akkako/akaLinkPro/firmware/application_5301/boards/akaLinkPro/pinmux.c

/*
 * Copyright (c) 2026 HPMicro
 *
 * SPDX-License-Identifier: BSD-3-Clause
 *
 */

/*
 * Note:
 * PY and PZ IOs: if any SOC pin function needs to be routed to these IOs,
 * besides of IOC, PIOC/BIOC needs to be configured SOC_GPIO_X_xx, so that
 * expected SoC function can be enabled on these IOs.
 */

#include "pinmux.h"
#include "board.h"
#include "hpm_trgm_drv.h"
#include "hpm_gpio_drv.h"
#include "hpm_gpiom_drv.h"

/* 5V output enable for the level shifter supply (active high). */
#define POWER_5V_EN_PIN IOC_PAD_PB13

/* Status LEDs (active high). */
#define LED1_PIN IOC_PAD_PB11
#define LED2_PIN IOC_PAD_PB12

/* External reference voltage sense (10k/10k divider), ADC0.2. */
#define ADC_VREF_PIN IOC_PAD_PB10


static void gpiom_config_pin_to_gpio0(uint16_t gpio_index)
{
    gpiom_set_pin_controller(HPM_GPIOM,
                             GPIO_GET_PORT_INDEX(gpio_index),
                             GPIO_GET_PIN_INDEX(gpio_index),
                             gpiom_soc_gpio0);
    gpiom_enable_pin_visibility(HPM_GPIOM,
                                GPIO_GET_PORT_INDEX(gpio_index),
                                GPIO_GET_PIN_INDEX(gpio_index),
                                gpiom_soc_gpio0);
}

static void init_unused_pin_as_input_pull_down(uint16_t gpio_index)
{
    HPM_IOC->PAD[gpio_index].FUNC_CTL = IOC_PAD_FUNC_CTL_ALT_SELECT_SET(0);
    HPM_IOC->PAD[gpio_index].PAD_CTL = IOC_PAD_PAD_CTL_PE_SET(1) | IOC_PAD_PAD_CTL_PS_SET(0);

    gpiom_config_pin_to_gpio0(gpio_index);
    gpio_set_pin_input(HPM_GPIO0, GPIO_GET_PORT_INDEX(gpio_index), GPIO_GET_PIN_INDEX(gpio_index));
    
}

static void init_unused_pin_as_input_no_pull(uint16_t gpio_index)
{
    HPM_IOC->PAD[gpio_index].FUNC_CTL = IOC_PAD_FUNC_CTL_ALT_SELECT_SET(0);
    HPM_IOC->PAD[gpio_index].PAD_CTL = 0;

    gpiom_config_pin_to_gpio0(gpio_index);
    gpio_set_pin_input(HPM_GPIO0, GPIO_GET_PORT_INDEX(gpio_index), GPIO_GET_PIN_INDEX(gpio_index));
    
}

/**
 * @brief Set PY00-PY05 default function to PGPIO
 * @param None
 */
void init_py_pins_as_pgpio(void)
{
    HPM_PIOC->PAD[IOC_PAD_PY00].FUNC_CTL = PIOC_PY00_FUNC_CTL_PGPIO_Y_00;
    HPM_PIOC->PAD[IOC_PAD_PY01].FUNC_CTL = PIOC_PY01_FUNC_CTL_PGPIO_Y_01;
}

/**
 * @brief Init UART0 Console print pin
 * @param None
 */
void init_uart0_pins(void)
{
    HPM_IOC->PAD[IOC_PAD_PA00].FUNC_CTL = IOC_PA00_FUNC_CTL_UART0_TXD;
    HPM_IOC->PAD[IOC_PAD_PA01].FUNC_CTL = IOC_PA01_FUNC_CTL_UART0_RXD;
}

/*
 * configure pad setting: pull enable and pull down, schmitt trigger enable
 * enable schmitt trigger to eliminate jitter of pin used as button
 */
void init_button_pins(void)
{
    /* Button */
    HPM_IOC->PAD[IOC_PAD_PA10].FUNC_CTL = IOC_PAD_FUNC_CTL_ALT_SELECT_SET(0);
    HPM_IOC->PAD[IOC_PAD_PA10].PAD_CTL = IOC_PAD_PAD_CTL_HYS_SET(1) | IOC_PAD_PAD_CTL_PE_SET(1) | IOC_PAD_PAD_CTL_PS_SET(0);
}

/**
 * @brief Set the 5V output enable pin (PB13, active high).
 * @param on 1 = enable 5V output, 0 = disable
 */
void board_set_5v_output(uint8_t on)
{
    gpio_write_pin(HPM_GPIO0, GPIO_GET_PORT_INDEX(POWER_5V_EN_PIN), GPIO_GET_PIN_INDEX(POWER_5V_EN_PIN), on ? 1 : 0);
}

/**
 * @brief Init power control pin and enable the 5V output by default.
 * @param None
 */
void init_power_pins(void)
{
    HPM_IOC->PAD[POWER_5V_EN_PIN].FUNC_CTL = IOC_PAD_FUNC_CTL_ALT_SELECT_SET(0);
    HPM_IOC->PAD[POWER_5V_EN_PIN].PAD_CTL =
        IOC_PAD_PAD_CTL_HYS_SET(0) | // schmitt trigger disable
        IOC_PAD_PAD_CTL_PRS_SET(0) | // pull resistor 100k
        IOC_PAD_PAD_CTL_PS_SET(0) |  // pull down
        IOC_PAD_PAD_CTL_PE_SET(0) |  // pull disable
        IOC_PAD_PAD_CTL_KE_SET(0) |  // keeper disable
        IOC_PAD_PAD_CTL_OD_SET(0) |  // open drain disable
        IOC_PAD_PAD_CTL_SR_SET(1) |  // fast slew rate
        IOC_PAD_PAD_CTL_SPD_SET(3) | // fastest slew rate
        IOC_PAD_PAD_CTL_DS_SET(4);   // drive strength 39 ohm(3.3V)

    gpiom_config_pin_to_gpio0(POWER_5V_EN_PIN);
    gpio_set_pin_output(HPM_GPIO0, GPIO_GET_PORT_INDEX(POWER_5V_EN_PIN), GPIO_GET_PIN_INDEX(POWER_5V_EN_PIN));
    board_set_5v_output(1);
}

/**
 * @brief Init the status LED pins as push-pull GPIO outputs, both off.
 * @param None
 */
void init_led_pins(void)
{
    const uint16_t leds[2] = {LED1_PIN, LED2_PIN};

    for (uint32_t i = 0; i < 2; i++)
    {
        HPM_IOC->PAD[leds[i]].FUNC_CTL = IOC_PAD_FUNC_CTL_ALT_SELECT_SET(0);
        HPM_IOC->PAD[leds[i]].PAD_CTL =
            IOC_PAD_PAD_CTL_HYS_SET(0) | // schmitt trigger disable
            IOC_PAD_PAD_CTL_PRS_SET(0) | // pull resistor 100k
            IOC_PAD_PAD_CTL_PS_SET(0) |  // pull down
            IOC_PAD_PAD_CTL_PE_SET(0) |  // pull disable
            IOC_PAD_PAD_CTL_KE_SET(0) |  // keeper disable
            IOC_PAD_PAD_CTL_OD_SET(0) |  // open drain disable
            IOC_PAD_PAD_CTL_SR_SET(1) |  // fast slew rate
            IOC_PAD_PAD_CTL_SPD_SET(3) | // fastest slew rate
            IOC_PAD_PAD_CTL_DS_SET(4);   // drive strength 39 ohm(3.3V)

        gpiom_config_pin_to_gpio0(leds[i]);
        gpio_set_pin_output(HPM_GPIO0, GPIO_GET_PORT_INDEX(leds[i]), GPIO_GET_PIN_INDEX(leds[i]));
        gpio_write_pin(HPM_GPIO0, GPIO_GET_PORT_INDEX(leds[i]), GPIO_GET_PIN_INDEX(leds[i]), 0);
    }
}

/**
 * @brief Init the external reference sense pin as ADC analog input.
 * @param None
 */
void init_adc_vref_pin(void)
{
    HPM_IOC->PAD[ADC_VREF_PIN].FUNC_CTL = IOC_PAD_FUNC_CTL_ANALOG_MASK;
}

/**
 * @brief Init USB0 pins
 * @param None
 */
void init_usb0_pins(void)
{
    HPM_IOC->PAD[IOC_PAD_PA24].FUNC_CTL = IOC_PAD_FUNC_CTL_ANALOG_MASK;

    HPM_IOC->PAD[IOC_PAD_PA25].FUNC_CTL = IOC_PAD_FUNC_CTL_ANALOG_MASK;

    /* USB0_ID */
    HPM_IOC->PAD[IOC_PAD_PY00].FUNC_CTL = IOC_PY00_FUNC_CTL_USB0_ID;
    HPM_PIOC->PAD[IOC_PAD_PY00].FUNC_CTL = PIOC_PY00_FUNC_CTL_SOC_GPIO_Y_00;

    /* USB0_OC */
    HPM_IOC->PAD[IOC_PAD_PY01].FUNC_CTL = IOC_PY01_FUNC_CTL_USB0_OC;
    HPM_PIOC->PAD[IOC_PAD_PY01].FUNC_CTL = PIOC_PY01_FUNC_CTL_SOC_GPIO_Y_01;
}

/**
 * @brief Init UART3 as VCOM port
 * @param None
 */
void init_uart3_pins_as_uart(void)
{
    // HPM_IOC->PAD[IOC_PAD_PB15].FUNC_CTL = IOC_PB15_FUNC_CTL_UART3_TXD;
    // HPM_IOC->PAD[IOC_PAD_PB14].FUNC_CTL = IOC_PB14_FUNC_CTL_UART3_RXD;
}

/*
 * for uart_lin case, need to configure pin as gpio to sent break signal
 * pull-up
 */
void init_uart3_pin_as_gpio_low(void)
{
    // HPM_IOC->PAD[BOARD_PIN_UART_TXD].FUNC_CTL = IOC_PAD_FUNC_CTL_ALT_SELECT_SET(0);
    // HPM_IOC->PAD[BOARD_PIN_UART_TXD].PAD_CTL = IOC_PAD_PAD_CTL_PE_SET(1) | IOC_PAD_PAD_CTL_PS_SET(0);

    // HPM_IOC->PAD[BOARD_PIN_UART_RXD].FUNC_CTL = IOC_PAD_FUNC_CTL_ALT_SELECT_SET(0);
    // HPM_IOC->PAD[BOARD_PIN_UART_RXD].PAD_CTL = IOC_PAD_PAD_CTL_PE_SET(1) | IOC_PAD_PAD_CTL_PS_SET(0);

    // HPM_IOC->PAD[BOARD_PIN_UART_RTS].FUNC_CTL = IOC_PAD_FUNC_CTL_ALT_SELECT_SET(0);
    // HPM_IOC->PAD[BOARD_PIN_UART_RTS].PAD_CTL = IOC_PAD_PAD_CTL_PE_SET(1) | IOC_PAD_PAD_CTL_PS_SET(0);

    // HPM_IOC->PAD[BOARD_PIN_UART_DTR].FUNC_CTL = IOC_PAD_FUNC_CTL_ALT_SELECT_SET(0);
    // HPM_IOC->PAD[BOARD_PIN_UART_DTR].PAD_CTL = IOC_PAD_PAD_CTL_PE_SET(1) | IOC_PAD_PAD_CTL_PS_SET(0);

    // gpiom_config_pin_to_gpio0(BOARD_PIN_UART_TXD);
    // gpiom_config_pin_to_gpio0(BOARD_PIN_UART_RXD);
    // gpiom_config_pin_to_gpio0(BOARD_PIN_UART_RTS);
    // gpiom_config_pin_to_gpio0(BOARD_PIN_UART_DTR);

    // gpio_set_pin_output(HPM_GPIO0, GPIO_GET_PORT_INDEX(BOARD_PIN_UART_TXD), GPIO_GET_PIN_INDEX(BOARD_PIN_UART_TXD));
    // gpio_set_pin_output(HPM_GPIO0, GPIO_GET_PORT_INDEX(BOARD_PIN_UART_RTS), GPIO_GET_PIN_INDEX(BOARD_PIN_UART_RTS));
    // gpio_set_pin_output(HPM_GPIO0, GPIO_GET_PORT_INDEX(BOARD_PIN_UART_DTR), GPIO_GET_PIN_INDEX(BOARD_PIN_UART_DTR));
    // gpio_set_pin_input(HPM_GPIO0, GPIO_GET_PORT_INDEX(BOARD_PIN_UART_RXD), GPIO_GET_PIN_INDEX(BOARD_PIN_UART_RXD));

    // gpio_write_pin(HPM_GPIO0, GPIO_GET_PORT_INDEX(BOARD_PIN_UART_TXD), GPIO_GET_PIN_INDEX(BOARD_PIN_UART_TXD), 0);
    // gpio_write_pin(HPM_GPIO0, GPIO_GET_PORT_INDEX(BOARD_PIN_UART_RTS), GPIO_GET_PIN_INDEX(BOARD_PIN_UART_RTS), 0);
    // gpio_write_pin(HPM_GPIO0, GPIO_GET_PORT_INDEX(BOARD_PIN_UART_DTR), GPIO_GET_PIN_INDEX(BOARD_PIN_UART_DTR), 0);
}

/*
 * @brief Init unused pins as input
 * @param None
 */
void init_unused_pin_as_input(void)
{
    // init_unused_pin_as_input_pull_down(BOARD_PIN_UNUSED_PORTEN);
    // init_unused_pin_as_input_pull_down(BOARD_PIN_UNUSED_PWM);
    // init_unused_pin_as_input_pull_down(BOARD_PIN_UNUSED_CS1);
    // init_unused_pin_as_input_pull_down(BOARD_PIN_UNUSED_CS2);
    // init_unused_pin_as_input_pull_down(BOARD_PIN_UNUSED_PEN);
    // init_unused_pin_as_input_pull_down(BOARD_PIN_UNUSED_VREF);
    // init_unused_pin_as_input_pull_down(BOARD_PIN_UNUSED_TVCC);
    // init_unused_pin_as_input_no_pull(BOARD_PIN_UNUSED_JTCK);
}

/**
 * @brief Init JTAG SWD pins as default state
 * @param None
 */
void init_jtag_swd_pin(void)
{
}
