akkako/akaLinkPro/firmware/application_5301/src/dap/SW_DP/SW_DP.c

/*
 * Copyright (c) 2013-2017 ARM Limited. All rights reserved.
 *
 * SPDX-License-Identifier: Apache-2.0
 *
 * Licensed under the Apache License, Version 2.0 (the License); you may
 * not use this file except in compliance with the License.
 * You may obtain a copy of the License at
 *
 * www.apache.org/licenses/LICENSE-2.0
 *
 * Unless required by applicable law or agreed to in writing, software
 * distributed under the License is distributed on an AS IS BASIS, WITHOUT
 * WARRANTIES OR CONDITIONS OF ANY KIND, either express or implied.
 * See the License for the specific language governing permissions and
 * limitations under the License.
 *
 * ----------------------------------------------------------------------
 *
 * $Date:        1. December 2017
 * $Revision:    V2.0.0
 *
 * Project:      CMSIS-DAP Source
 * Title:        SW_DP.c CMSIS-DAP SW DP I/O
 *
 *---------------------------------------------------------------------------*/

#include "DAP_config.h"
#include "DAP.h"
#include "SW_DP.h"
#include "hpm_common.h"

#define SWJ_SEQUENCE_OFFSET_60M 0x00000000
#define SWD_WRITE_OFFSET_60M 0x000000fc
#define SWD_READ_OFFSET_60M 0x0000053c

#define SWJ_SEQUENCE_OFFSET_45M 0x00000000
#define SWD_WRITE_OFFSET_45M 0x00000120
#define SWD_READ_OFFSET_45M 0x0000060c

#define SWJ_SEQUENCE_OFFSET_36M 0x00000000
#define SWD_WRITE_OFFSET_36M 0x00000144
#define SWD_READ_OFFSET_36M 0x000006e0

#define SWJ_SEQUENCE_OFFSET_30M 0x00000000
#define SWD_WRITE_OFFSET_30M 0x0000016c
#define SWD_READ_OFFSET_30M 0x000007c4

#define SWJ_SEQUENCE_OFFSET_20M 0x00000000
#define SWD_WRITE_OFFSET_20M 0x000001d8
#define SWD_READ_OFFSET_20M 0x00000a54

#define SWJ_SEQUENCE_OFFSET_SLOW 0x00000010
#define SWD_WRITE_OFFSET_SLOW 0x00000138
#define SWD_READ_OFFSET_SLOW 0x00000620

// clang-format off
const uint8_t swd_func_60m[2584] =
{
	0xB7, 0x02, 0x0C, 0x00, 0x37, 0x03, 0x00, 0x40, 0xB7, 0x03, 0x00, 0x08, 0x93, 0x56, 0x35, 0x00,
    0x13, 0x77, 0x75, 0x00, 0xE1, 0xC2, 0x03, 0xC8, 0x05, 0x00, 0x85, 0x05, 0x13, 0x7E, 0x18, 0x00,
    0x72, 0x0E, 0x33, 0x6E, 0x6E, 0x00, 0x23, 0xA0, 0xC2, 0x11, 0x13, 0x58, 0x18, 0x00, 0x13, 0x7E,
    0x18, 0x00, 0x23, 0xA2, 0x72, 0x10, 0x72, 0x0E, 0x33, 0x6E, 0x6E, 0x00, 0x23, 0xA0, 0xC2, 0x11,
    0x13, 0x58, 0x18, 0x00, 0x13, 0x7E, 0x18, 0x00, 0x23, 0xA2, 0x72, 0x10, 0x72, 0x0E, 0x33, 0x6E,
    0x6E, 0x00, 0x23, 0xA0, 0xC2, 0x11, 0x13, 0x58, 0x18, 0x00, 0x13, 0x7E, 0x18, 0x00, 0x23, 0xA2,
    0x72, 0x10, 0x72, 0x0E, 0x33, 0x6E, 0x6E, 0x00, 0x23, 0xA0, 0xC2, 0x11, 0x13, 0x58, 0x18, 0x00,
    0x13, 0x7E, 0x18, 0x00, 0x23, 0xA2, 0x72, 0x10, 0x72, 0x0E, 0x33, 0x6E, 0x6E, 0x00, 0x23, 0xA0,
    0xC2, 0x11, 0x13, 0x58, 0x18, 0x00, 0x13, 0x7E, 0x18, 0x00, 0x23, 0xA2, 0x72, 0x10, 0x72, 0x0E,
    0x33, 0x6E, 0x6E, 0x00, 0x23, 0xA0, 0xC2, 0x11, 0x13, 0x58, 0x18, 0x00, 0x13, 0x7E, 0x18, 0x00,
    0x23, 0xA2, 0x72, 0x10, 0x72, 0x0E, 0x33, 0x6E, 0x6E, 0x00, 0x23, 0xA0, 0xC2, 0x11, 0x13, 0x58,
    0x18, 0x00, 0x13, 0x7E, 0x18, 0x00, 0x23, 0xA2, 0x72, 0x10, 0x72, 0x0E, 0x33, 0x6E, 0x6E, 0x00,
    0x23, 0xA0, 0xC2, 0x11, 0x13, 0x58, 0x18, 0x00, 0x13, 0x7E, 0x18, 0x00, 0x23, 0xA2, 0x72, 0x10,
    0xFD, 0x16, 0xB1, 0xF2, 0x15, 0xC3, 0x03, 0xC8, 0x05, 0x00, 0x13, 0x7E, 0x18, 0x00, 0x72, 0x0E,
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

swd_sequence_ptr seq_func = NULL;
swd_write_ptr write_func = NULL;
swd_read_ptr read_func = NULL;

void SWD_DynamicLoad_Slow(void)
{
    memcpy(swd_ops, swd_func_slow, sizeof(swd_func_slow));
    __asm volatile("fence.i");

    seq_func = (swd_sequence_ptr)((uint32_t)swd_ops + SWJ_SEQUENCE_OFFSET_SLOW);
    write_func = (swd_write_ptr)((uint32_t)swd_ops + SWD_WRITE_OFFSET_SLOW);
    read_func = (swd_read_ptr)((uint32_t)swd_ops + SWD_READ_OFFSET_SLOW);
}

void SWD_DynamicLoad_60M(void)
{
    memcpy(swd_ops, swd_func_60m, sizeof(swd_func_60m));
    __asm volatile("fence.i");

    seq_func = (swd_sequence_ptr)((uint32_t)swd_ops + SWJ_SEQUENCE_OFFSET_60M);
    write_func = (swd_write_ptr)((uint32_t)swd_ops + SWD_WRITE_OFFSET_60M);
    read_func = (swd_read_ptr)((uint32_t)swd_ops + SWD_READ_OFFSET_60M);
}

void SWD_DynamicLoad_45M(void)
{
    memcpy(swd_ops, swd_func_45m, sizeof(swd_func_45m));
    __asm volatile("fence.i");

    seq_func = (swd_sequence_ptr)((uint32_t)swd_ops + SWJ_SEQUENCE_OFFSET_45M);
    write_func = (swd_write_ptr)((uint32_t)swd_ops + SWD_WRITE_OFFSET_45M);
    read_func = (swd_read_ptr)((uint32_t)swd_ops + SWD_READ_OFFSET_45M);
}

void SWD_DynamicLoad_36M(void)
{
    memcpy(swd_ops, swd_func_36m, sizeof(swd_func_36m));
    __asm volatile("fence.i");

    seq_func = (swd_sequence_ptr)((uint32_t)swd_ops + SWJ_SEQUENCE_OFFSET_36M);
    write_func = (swd_write_ptr)((uint32_t)swd_ops + SWD_WRITE_OFFSET_36M);
    read_func = (swd_read_ptr)((uint32_t)swd_ops + SWD_READ_OFFSET_36M);
}

void SWD_DynamicLoad_30M(void)
{
    memcpy(swd_ops, swd_func_30m, sizeof(swd_func_30m));
    __asm volatile("fence.i");

    seq_func = (swd_sequence_ptr)((uint32_t)swd_ops + SWJ_SEQUENCE_OFFSET_30M);
    write_func = (swd_write_ptr)((uint32_t)swd_ops + SWD_WRITE_OFFSET_30M);
    read_func = (swd_read_ptr)((uint32_t)swd_ops + SWD_READ_OFFSET_30M);
}

void SWD_DynamicLoad_20M(void)
{
    memcpy(swd_ops, swd_func_20m, sizeof(swd_func_20m));
    __asm volatile("fence.i");

    seq_func = (swd_sequence_ptr)((uint32_t)swd_ops + SWJ_SEQUENCE_OFFSET_20M);
    write_func = (swd_write_ptr)((uint32_t)swd_ops + SWD_WRITE_OFFSET_20M);
    read_func = (swd_read_ptr)((uint32_t)swd_ops + SWD_READ_OFFSET_20M);
}

#if ((DAP_SWD != 0) || (DAP_JTAG != 0))
/**
 * @brief Generate SWJ Sequence
 * @param count sequence bit count
 * @param data pointer to sequence bit data
 * @return none
 */
ATTR_RAMFUNC void SWJ_Sequence(uint32_t count, const uint8_t *data)
{
    seq_func(count, data, DAP_Data.clock_delay);
}
#endif

#if (DAP_SWD != 0)
/**
 * @brief Generate SWD Sequence
 * @param info sequence information
 * @param swdo pointer to SWDIO generated data
 * @param swdi pointer to SWDIO captured data
 * @return none
 */
ATTR_RAMFUNC void SWD_Sequence(uint32_t info, const uint8_t *swdo, uint8_t *swdi)
{
    // SWD_Sequence_GPIO_Fast(info, swdo, swdi);
    SWD_Sequence_GPIO_Slow(info, swdo, swdi);
}
#endif

/**
 * @brief SWD Write
 * @param request A[3:2] RnW APnDP
 * @param data DATA[31:0]
 * @return ACK[2:0]
 */
ATTR_RAMFUNC uint8_t SWD_Write(uint32_t request, uint32_t *data)
{
    uint8_t header = 0x81 | ((request & 0x0F) << 1) | (((request ^ (request >> 1) ^ (request >> 2) ^ (request >> 3)) & 1) << 5);

    uint8_t ack = write_func(header, data, DAP_Data.clock_delay);
    if (request & DAP_TRANSFER_TIMESTAMP)
    {
        DAP_Data.timestamp = TIMESTAMP_GET();
    }
    return ack;
}

/**
 * @brief SWD Read
 * @param request A[3:2] RnW APnDP
 * @param data DATA[31:0]
 * @return ACK[2:0]
 */
ATTR_RAMFUNC uint8_t SWD_Read(uint32_t request, uint32_t *data)
{
    uint8_t header = 0x81 | ((request & 0x0F) << 1) | (((request ^ (request >> 1) ^ (request >> 2) ^ (request >> 3)) & 1) << 5);

    uint8_t ack = read_func(header, data, DAP_Data.clock_delay);
    if (request & DAP_TRANSFER_TIMESTAMP)
    {
        DAP_Data.timestamp = TIMESTAMP_GET();
    }
    return ack;
}
