akkako/akaLinkPro/firmware/application_5301/boards/akaLinkPro/board.c

/*
 * Copyright (c) 2023-2026 HPMicro
 * SPDX-License-Identifier: BSD-3-Clause
 *
 */

#include "board.h"
#include "clock.h"
#include "hpm_uart_drv.h"
#include "hpm_sdk_version.h"
#include "hpm_gptmr_drv.h"
#include "hpm_gpio_drv.h"
#include "hpm_usb_drv.h"
#include "hpm_clock_drv.h"
#include "hpm_pllctlv2_drv.h"
#include "hpm_i2c_drv.h"
#include "hpm_pcfg_drv.h"

/**
 * @brief FLASH configuration option definitions:
 * option[0]:
 *    [31:16] 0xfcf9 - FLASH configuration option tag
 *    [15:4]  0 - Reserved
 *    [3:0]   option words (exclude option[0])
 * option[1]:
 *    [31:28] Flash probe type
 *      0 - SFDP SDR / 1 - SFDP DDR
 *      2 - 1-4-4 Read (0xEB, 24-bit address) / 3 - 1-2-2 Read(0xBB, 24-bit address)
 *      4 - HyperFLASH 1.8V / 5 - HyperFLASH 3V
 *      6 - OctaBus DDR (SPI -> OPI DDR)
 *      8 - Xccela DDR (SPI -> OPI DDR)
 *      10 - EcoXiP DDR (SPI -> OPI DDR)
 *    [27:24] Command Pads after Power-on Reset
 *      0 - SPI / 1 - DPI / 2 - QPI / 3 - OPI
 *    [23:20] Command Pads after Configuring FLASH
 *      0 - SPI / 1 - DPI / 2 - QPI / 3 - OPI
 *    [19:16] Quad Enable Sequence (for the device support SFDP 1.0 only)
 *      0 - Not needed
 *      1 - QE bit is at bit 6 in Status Register 1
 *      2 - QE bit is at bit1 in Status Register 2
 *      3 - QE bit is at bit7 in Status Register 2
 *      4 - QE bit is at bit1 in Status Register 2 and should be programmed by 0x31
 *    [15:8] Dummy cycles
 *      0 - Auto-probed / detected / default value
 *      Others - User specified value, for DDR read, the dummy cycles should be 2 * cycles on FLASH datasheet
 *    [7:4] Misc.
 *      0 - Not used
 *      1 - SPI mode
 *      2 - Internal loopback
 *      3 - External DQS
 *    [3:0] Frequency option
 *      1 - 30MHz / 2 - 50MHz / 3 - 66MHz / 4 - 80MHz / 5 - 100MHz / 6 - 114MHz / 7 - 133MHz / 8 - 166MHz
 *
 * option[2] (Effective only if the bit[3:0] in option[0] > 1)
 *    [31:20]  Reserved
 *    [19:16] IO voltage
 *      0 - 3V / 1 - 1.8V
 *    [15:12] Pin group
 *      0 - 1st group / 1 - 2nd group
 *    [11:8] Connection selection
 *      0 - CA_CS0 / 1 - CB_CS0 / 2 - CA_CS0 + CB_CS0 (Two FLASH connected to CA and CB respectively)
 *    [7:0] Drive Strength
 *      0 - Default value
 * option[3] (Effective only if the bit[3:0] in option[0] > 2, required only for the QSPI NOR FLASH that not supports
 *              JESD216)
 *    [31:16] reserved
 *    [15:12] Sector Erase Command Option, not required here
 *    [11:8]  Sector Size Option, not required here
 *    [7:0] Flash Size Option
 *      0 - 4MB / 1 - 8MB / 2 - 16MB
 */
#if defined(FLASH_XIP) && FLASH_XIP
__attribute__ ((section(".nor_cfg_option"), used)) const uint32_t option[4] = {0xfcf90002, 0x00000005, 0x1000, 0x0};
#endif

#if defined(FLASH_UF2) && FLASH_UF2
ATTR_PLACE_AT(".uf2_signature") __attribute__((used)) const uint32_t uf2_signature = BOARD_UF2_SIGNATURE;
#endif

#if defined(FLASH_DFU) && FLASH_DFU
ATTR_PLACE_AT(".dfu_signature") __attribute__((used)) const uint32_t dfu_signature = BOARD_DFU_SIGNATURE;
#endif

void board_init_console(void)
{
#if !defined(CONFIG_NDEBUG_CONSOLE) || !CONFIG_NDEBUG_CONSOLE
#if BOARD_CONSOLE_TYPE == CONSOLE_TYPE_UART
    console_config_t cfg;

    /* uart needs to configure pin function before enabling clock, otherwise the level change of
     * uart rx pin when configuring pin function will cause a wrong data to be received.
     * And a uart rx dma request will be generated by default uart fifo dma trigger level.
     */
    init_uart_pins((UART_Type *) BOARD_CONSOLE_UART_BASE);

    init_uart0_clock();

    cfg.type = BOARD_CONSOLE_TYPE;
    cfg.base = (uint32_t)BOARD_CONSOLE_UART_BASE;
    cfg.src_freq_in_hz = clock_get_frequency(BOARD_CONSOLE_UART_CLK_NAME);
    cfg.baudrate = BOARD_CONSOLE_UART_BAUDRATE;

    if (status_success != console_init(&cfg)) {
        /* failed to  initialize debug console */
        while (1) {
        }
    }
#else
    while (1)
        ;
#endif
#endif
}

void board_print_banner(void)
{
    const uint8_t banner[] = "\n"
"----------------------------------------------------------------------\n"
"$$\\   $$\\ $$$$$$$\\  $$\\      $$\\ $$\\\n"
"$$ |  $$ |$$  __$$\\ $$$\\    $$$ |\\__|\n"
"$$ |  $$ |$$ |  $$ |$$$$\\  $$$$ |$$\\  $$$$$$$\\  $$$$$$\\   $$$$$$\\\n"
"$$$$$$$$ |$$$$$$$  |$$\\$$\\$$ $$ |$$ |$$  _____|$$  __$$\\ $$  __$$\\\n"
"$$  __$$ |$$  ____/ $$ \\$$$  $$ |$$ |$$ /      $$ |  \\__|$$ /  $$ |\n"
"$$ |  $$ |$$ |      $$ |\\$  /$$ |$$ |$$ |      $$ |      $$ |  $$ |\n"
"$$ |  $$ |$$ |      $$ | \\_/ $$ |$$ |\\$$$$$$$\\ $$ |      \\$$$$$$  |\n"
"\\__|  \\__|\\__|      \\__|     \\__|\\__| \\_______|\\__|       \\______/\n"
"----------------------------------------------------------------------\n";
#ifdef SDK_VERSION_STRING
    printf("hpm_sdk: %s\n", SDK_VERSION_STRING);
#endif
    printf("%s", banner);
}

void board_print_clock_freq(void)
{
    printf("==============================\n");
    printf(" %s clock summary\n", BOARD_NAME);
    printf("==============================\n");
    printf("cpu0:\t\t %luHz\n", clock_get_frequency(clock_cpu0));
    printf("ahb:\t\t %luHz\n", clock_get_frequency(clock_ahb));
    printf("mchtmr0:\t %luHz\n", clock_get_frequency(clock_mchtmr0));
    printf("xpi0:\t\t %luHz\n", clock_get_frequency(clock_xpi0));
    printf("==============================\n");
}

void board_init(void)
{
    init_py_pins_as_pgpio();
    board_init_gpio_pins();
    board_init_usb_dp_dm_pins();

    board_init_clock();
    board_init_console();
    board_init_pmp();
#if BOARD_SHOW_CLOCK
    board_print_clock_freq();
#endif
#if BOARD_SHOW_BANNER
    board_print_banner();
#endif
}

void board_init_usb_dp_dm_pins(void)
{
    /* Disconnect usb dp/dm pins pull down 45ohm resistance */

    while (sysctl_resource_any_is_busy(HPM_SYSCTL)) {
        ;
    }
    if (pllctlv2_xtal_is_stable(HPM_PLLCTLV2) && pllctlv2_xtal_is_enabled(HPM_PLLCTLV2)) {
        if (clock_check_in_group(clock_usb0, 0)) {
            usb_phy_disable_dp_dm_pulldown(HPM_USB0);
        } else {
            init_usb0_clock();
            usb_phy_disable_dp_dm_pulldown(HPM_USB0);
            clock_remove_from_group(clock_usb0, 0);
        }
    } else {
        uint8_t tmp;
        tmp = sysctl_resource_target_get_mode(HPM_SYSCTL, sysctl_resource_xtal);
        sysctl_resource_target_set_mode(HPM_SYSCTL, sysctl_resource_xtal, 0x03);    /* NOLINT */
        init_usb0_clock();
        usb_phy_disable_dp_dm_pulldown(HPM_USB0);
        clock_remove_from_group(clock_usb0, 0);
        while (sysctl_resource_target_is_busy(HPM_SYSCTL, sysctl_resource_usb0)) {
            ;
        }
        sysctl_resource_target_set_mode(HPM_SYSCTL, sysctl_resource_xtal, tmp);
    }
}

void board_init_clock(void)
{
    uint32_t cpu0_freq = clock_get_frequency(clock_cpu0);

    if (cpu0_freq == PLLCTL_SOC_PLL_REFCLK_FREQ) {
        /* Configure the External OSC ramp-up time: ~9ms */
        pllctlv2_xtal_set_rampup_time(HPM_PLLCTLV2, 32UL * 1000UL * 9U);

        /* Select clock setting preset1 */
        sysctl_clock_set_preset(HPM_SYSCTL, 2);
    }

    /* select XTAL as pll ref clock */
    pllctlv2_select_reference_clock(HPM_PLLCTLV2, pllctlv2_pll0, 0);
    pllctlv2_select_reference_clock(HPM_PLLCTLV2, pllctlv2_pll1, 0);

    /* group0[0], clock_mot0 is for trgm and synt peripheral */
    init_board_clock();

    /* Connect Group0 to CPU0 */
    clock_connect_group_to_cpu(0, 0);

    /* Note: When using an external DCDC, don't set the internal DCDC voltage. The following call of pcfg_dcdc_set_voltage() function should be commented out. */
    /* Bump up DCDC voltage to 1175mv */
    pcfg_dcdc_set_voltage(HPM_PCFG, 1175);

    /* Configure CPU to 360MHz, AXI/AHB to 120MHz */
    sysctl_config_cpu0_domain_clock(HPM_SYSCTL, clock_source_pll0_clk0, 2, 3);
    /* Configure PLL0 Post Divider */
    /* PLL0CLK0: 720MHz */
    /* PLL0CLK1: 600MHz */
    /* PLL0CLK2: 400MHz */
    /* Configure PLL0 Frequency to 720MHz */
    /* Configure mchtmr to 24MHz */
    init_board_clock_source();

    clock_update_core_clock();
}

void board_delay_us(uint32_t us)
{
    clock_cpu_delay_us(us);
}

void board_delay_ms(uint32_t ms)
{
    clock_cpu_delay_ms(ms);
}

void board_init_gpio_pins(void)
{
    init_button_pins();
    init_unused_pin_as_input();
    init_uart3_pin_as_gpio_low();
    /* Enable the 5V level-shifter supply by default (PB13 high). */
    init_power_pins();
    /* Status LEDs (PB11/PB12) and external reference ADC pin (PB10). */
    init_led_pins();
    init_adc_vref_pin();
    gpio_set_pin_input(BOARD_APP_GPIO_CTRL, BOARD_APP_GPIO_INDEX, BOARD_APP_GPIO_PIN);
}

void board_init_usb(USB_Type *ptr)
{
    if (ptr == HPM_USB0) {
        init_usb_pins(ptr);
        init_usb0_clock();

        usb_hcd_set_power_ctrl_polarity(ptr, true);
        /* Wait USB_PWR pin control vbus power stable. Time depend on decoupling capacitor, you can decrease or increase this time */
        board_delay_ms(100);

        /* As QFN48 and LQFP64 has no vbus pin, so should be call usb_phy_using_internal_vbus() API to use internal vbus. */
        usb_phy_using_internal_vbus(ptr);
    }
}

void board_init_uart(UART_Type *ptr)
{
    /* configure uart's pin before opening uart's clock */
    init_uart_pins(ptr);
    board_init_uart_clock(ptr);
}

void board_ungate_mchtmr_at_lp_mode(void)
{
    /* Keep cpu clock on wfi, so that mchtmr irq can still work after wfi */
    sysctl_set_cpu_lp_mode(HPM_SYSCTL, BOARD_RUNNING_CORE, cpu_lp_mode_ungate_cpu_clock);
}

void board_init_pmp(void)
{
}

uint32_t board_init_uart_clock(UART_Type *ptr)
{
    uint32_t freq = 0U;
    if (ptr == HPM_UART0) {
        init_uart0_clock();
        freq = clock_get_frequency(clock_uart0);
    } else if (ptr == HPM_UART3) {
        init_uart3_clock();
        freq = clock_get_frequency(clock_uart3);
    }

    return freq;
}
void init_uart_pins(UART_Type *ptr)
{
    if (ptr == HPM_UART0) {
        init_uart0_pins();
    } else if (ptr == HPM_UART3) {
        init_uart3_pins_as_uart();
    } else {
        ;
    }
}


void init_usb_pins(USB_Type *ptr)
{
    if (ptr == HPM_USB0) {
        init_usb0_pins();
    }
}
