akkako/akaLinkPro/firmware/application_5301/src/dap/SW_DP/SW_DP.h

#ifndef SW_DP_H
#define SW_DP_H

#include <stdint.h>

uint32_t swd_speed_calc(uint32_t xq);

void SWJ_Sequence_GPIO_Slow(uint32_t count, const uint8_t *data);
void SWD_Sequence_GPIO_Slow(uint32_t info, const uint8_t *swdo, uint8_t *swdi);
uint8_t SWD_Write_GPIO_Slow(uint8_t header, uint32_t *data);
uint8_t SWD_Read_GPIO_Slow(uint8_t header, uint32_t *data);

void SWJ_Sequence_GPIO_ASM_20M(uint32_t count, const uint8_t *data, uint32_t delay);
uint8_t SWD_Write_GPIO_ASM_20M(uint8_t header, uint32_t *data, uint32_t delay);
uint8_t SWD_Read_GPIO_ASM_20M(uint8_t header, uint32_t *data, uint32_t delay);

void SWJ_Sequence_GPIO_ASM_30M(uint32_t count, const uint8_t *data, uint32_t delay);
uint8_t SWD_Write_GPIO_ASM_30M(uint8_t header, uint32_t *data, uint32_t delay);
uint8_t SWD_Read_GPIO_ASM_30M(uint8_t header, uint32_t *data, uint32_t delay);

void SWJ_Sequence_GPIO_ASM_36M(uint32_t count, const uint8_t *data, uint32_t delay);
uint8_t SWD_Write_GPIO_ASM_36M(uint8_t header, uint32_t *data, uint32_t delay);
uint8_t SWD_Read_GPIO_ASM_36M(uint8_t header, uint32_t *data, uint32_t delay);

void SWJ_Sequence_GPIO_ASM_45M(uint32_t count, const uint8_t *data, uint32_t delay);
uint8_t SWD_Write_GPIO_ASM_45M(uint8_t header, uint32_t *data, uint32_t delay);
uint8_t SWD_Read_GPIO_ASM_45M(uint8_t header, uint32_t *data, uint32_t delay);

void SWJ_Sequence_GPIO_ASM_60M(uint32_t count, const uint8_t *data, uint32_t delay);
uint8_t SWD_Write_GPIO_ASM_60M(uint8_t header, uint32_t *data, uint32_t delay);
uint8_t SWD_Read_GPIO_ASM_60M(uint8_t header, uint32_t *data, uint32_t delay);

void SWJ_Sequence_GPIO_ASM_SLOW(uint32_t count, const uint8_t *data, uint32_t delay);
uint8_t SWD_Write_GPIO_ASM_SLOW(uint8_t header, uint32_t *data, uint32_t delay);
uint8_t SWD_Read_GPIO_ASM_SLOW(uint8_t header, uint32_t *data, uint32_t delay);

void SWD_DynamicLoad_Slow(void);
void SWD_DynamicLoad_60M(void);
void SWD_DynamicLoad_45M(void);
void SWD_DynamicLoad_36M(void);
void SWD_DynamicLoad_30M(void);
void SWD_DynamicLoad_20M(void);

#endif
