akkako/akaLinkPro/firmware/application_5301/src/dap/SW_DP/SW_SPEED_CALC.c

/**
 * @file  loglog_interp.c
 * @brief 输入输出均x1000缩放的 log-log 分段线性插值 (Q16.16定点, 无浮点)
 *        标定数据: x: 35.91~15380, y: 1~1000
 *        限制输入范围: 缩放前 x ∈ [10, 16000] -> 缩放后 xq ∈ [10000, 16000000]
 *        输出 yq ∈ [1000, 1000000] (对应缩放前 y ∈ [1, 1000])
 */
#include <stdint.h>

#define Q16_16(x)   ((int32_t)((x) * 65536.0 + ((x) >= 0 ? 0.5 : -0.5)))
#define LN2_Q16     45426u   /* ln(2) * 65536 */

/* ln(1 + k/256), k = 0..256, Q16.16 */
static const uint32_t LN_LUT[257] = {
         0,    256,    510,    764,   1016,   1268,   1518,   1768,
      2017,   2264,   2511,   2757,   3002,   3246,   3489,   3732,
      3973,   4214,   4453,   4692,   4930,   5167,   5403,   5638,
      5873,   6106,   6339,   6571,   6802,   7033,   7262,   7491,
      7719,   7946,   8173,   8398,   8623,   8847,   9070,   9293,
      9515,   9736,   9956,  10176,  10394,  10612,  10830,  11046,
     11262,  11478,  11692,  11906,  12119,  12332,  12543,  12754,
     12965,  13174,  13383,  13592,  13800,  14007,  14213,  14419,
     14624,  14828,  15032,  15235,  15438,  15640,  15841,  16042,
     16242,  16442,  16641,  16839,  17037,  17234,  17430,  17626,
     17821,  18016,  18210,  18404,  18597,  18790,  18981,  19173,
     19364,  19554,  19743,  19933,  20121,  20309,  20497,  20684,
     20870,  21056,  21241,  21426,  21611,  21795,  21978,  22161,
     22343,  22525,  22706,  22887,  23067,  23247,  23426,  23605,
     23783,  23961,  24139,  24315,  24492,  24668,  24843,  25018,
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
static const int32_t NODE_LNY[10] = { 905413, 859987, 754511, 709085, 603609, 558183, 543559, 524705, 498133, 452707 };

#define XQ_MIN   10000u       /* 缩放后输入下限 (缩放前 10)   */
#define XQ_MAX   16000000u    /* 缩放后输入上限 (缩放前 16000) */
#define YQ_MIN   1000u
#define YQ_MAX   1000000u

/** 定点自然对数: ln(v), v >= 1, 结果 Q16.16 */
static int32_t fp_ln(uint32_t v)
{
    int e = 31 - __builtin_clz(v);        /* v = m * 2^e, m in [1,2) */
    uint32_t m = v << __builtin_clz(v);   /* Q1.31 */
    uint32_t k8   = (m >> 23) - 256;      /* mantissa-1 in [0,1) -> 0..255 */
    uint32_t frac = (m >> 15) & 0xFF;     /* 低8位做插值 */
    uint32_t f = LN_LUT[k8] +
        (uint32_t)(((uint64_t)(LN_LUT[k8+1] - LN_LUT[k8]) * frac) >> 8);
    return (int32_t)(e * LN2_Q16 + f);
}

/** 定点指数: exp(t), t 为 Q16.16, 结果 = 实际值 * 65536 */
static uint32_t fp_exp(int32_t t)
{
    uint32_t k  = (uint32_t)t / LN2_Q16;         /* t = k*ln2 + r */
    uint32_t r  = (uint32_t)t - k * LN2_Q16;     /* r in [0, ln2) */
    uint32_t f  = (uint32_t)(((uint64_t)r << 16) / LN2_Q16);  /* r/ln2, Q16.16, [0,1) */
    uint32_t j  = f >> 8;                        /* 0..255 */
    uint32_t fr = f & 0xFF;
    uint32_t g  = POW2_LUT[j] +
        (uint32_t)(((uint64_t)(POW2_LUT[j+1] - POW2_LUT[j]) * fr) >> 8);
    /* y = g * 2^k / 65536 */
    return (uint32_t)((((uint64_t)g << k) + 0x8000u) >> 16);
}

/**
 * @brief  log-log 分段线性插值
 * @param  xq 输入, 已x1000缩放, 范围 [10000, 16000000], 超范围自动钳位
 * @return yq 输出, 已x1000缩放
 */
uint32_t swd_speed_calc(uint32_t xq)
{
    if (xq < XQ_MIN) xq = XQ_MIN;
    if (xq > XQ_MAX) xq = XQ_MAX;

    int32_t lx = fp_ln(xq);
    if (lx <= NODE_LNX[0]) return YQ_MAX;   /* 低于最低标定点 */

    /* 二分查找: NODE_LNX 升序 */
    int lo = 0, hi = 9;
    while (hi - lo > 1) {
        int mid = (lo + hi) >> 1;
        if (NODE_LNX[mid] <= lx) lo = mid; else hi = mid;
    }
    if (lx >= NODE_LNX[9]) { lo = 8; hi = 9; }  /* 上端外插并入最后一段 */

    /* 区间内线性插值 */
    int32_t dx = NODE_LNX[hi] - NODE_LNX[lo];
    uint32_t frac = (uint32_t)(((uint64_t)(lx - NODE_LNX[lo]) << 16) / (uint32_t)dx);
    int32_t ly = NODE_LNY[lo] +
        (int32_t)(((int64_t)(NODE_LNY[hi] - NODE_LNY[lo]) * (int64_t)frac) >> 16);

    uint32_t yq = fp_exp(ly);
    if (yq < YQ_MIN) yq = YQ_MIN;
    if (yq > YQ_MAX) yq = YQ_MAX;
    return yq;
}
