akkako/akaLinkPro/firmware/bootloader_dfu/boards/akaLinkPro/board.h

/*
 * Copyright (c) 2023-2024 HPMicro
 *
 * SPDX-License-Identifier: BSD-3-Clause
 *
 */

#ifndef _HPM_BOARD_H
#define _HPM_BOARD_H

#include "hpm_clock_drv.h"
#include "hpm_common.h"
#include "hpm_soc.h"
#include "hpm_soc_feature.h"
#include "pinmux.h"
#include <hpm_ewdg_drv.h>
#include <stdarg.h>
#include <stdio.h>

#if !defined(CONFIG_NDEBUG_CONSOLE) || !CONFIG_NDEBUG_CONSOLE

#include "hpm_debug_console.h"

#endif

#define BOARD_NAME "akaLinkPro"
#define BOARD_UF2_SIGNATURE (0x0A4D5048UL)
#define BOARD_DFU_SIGNATURE (0x48504D21UL) /* "HPM!" */
#define BOARD_BGPR HPM_BGPR0

/* core section */
#ifndef BOARD_RUNNING_CORE
#define BOARD_RUNNING_CORE HPM_CORE0
#endif

#if !defined(CONFIG_NDEBUG_CONSOLE) || !CONFIG_NDEBUG_CONSOLE
#ifndef BOARD_CONSOLE_TYPE
#define BOARD_CONSOLE_TYPE CONSOLE_TYPE_UART
#endif

#if BOARD_CONSOLE_TYPE == CONSOLE_TYPE_UART
#ifndef BOARD_CONSOLE_UART_BASE
#define BOARD_CONSOLE_UART_BASE HPM_UART0
#define BOARD_CONSOLE_UART_CLK_NAME clock_uart0
#define BOARD_CONSOLE_UART_IRQ IRQn_UART0
#define BOARD_CONSOLE_UART_TX_DMA_REQ HPM_DMA_SRC_UART0_TX
#define BOARD_CONSOLE_UART_RX_DMA_REQ HPM_DMA_SRC_UART0_RX
#endif
#define BOARD_CONSOLE_UART_BAUDRATE (115200UL)
#endif
#endif

/* nor flash section */
#define BOARD_FLASH_BASE_ADDRESS (0x80000000UL) /* Check */
#define BOARD_FLASH_SIZE (SIZE_1MB)

/* Last two 4K sectors of the flash are reserved for the APP parameter store.
 * The DFU upgrade path must never erase or program this area. */
#define BOARD_PARAM_RESERVED_SIZE (0x2000UL)
#define BOARD_DFU_WRITABLE_SIZE (BOARD_FLASH_SIZE - BOARD_PARAM_RESERVED_SIZE)

/* gpiom section */
#define BOARD_APP_GPIOM_BASE HPM_GPIOM
#define BOARD_APP_GPIOM_USING_CTRL HPM_FGPIO
#define BOARD_APP_GPIOM_USING_CTRL_NAME gpiom_core0_fast

/* User button */
#define BOARD_APP_GPIO_CTRL HPM_GPIO0
#define BOARD_APP_GPIO_INDEX GPIO_DI_GPIOA
#define BOARD_APP_GPIO_PIN 10
#define BOARD_APP_GPIO_IRQ IRQn_GPIO0_A
#define BOARD_BTN_PRESSED_VALUE 1

/* Flash section */
#define BOARD_APP_XPI_NOR_XPI_BASE (HPM_XPI0)
#define BOARD_APP_XPI_NOR_CFG_OPT_HDR (0xfcf90002U)
#define BOARD_APP_XPI_NOR_CFG_OPT_OPT0 (0x00000006U)
#define BOARD_APP_XPI_NOR_CFG_OPT_OPT1 (0x00001000U)

/* CALLBACK TIMER section */
#define BOARD_CALLBACK_TIMER (HPM_GPTMR1)
#define BOARD_CALLBACK_TIMER_CH 0
#define BOARD_CALLBACK_TIMER_IRQ IRQn_GPTMR1
#define BOARD_CALLBACK_TIMER_CLK_NAME (clock_gptmr1)

#ifndef BOARD_SHOW_CLOCK
#define BOARD_SHOW_CLOCK 1
#endif

#if defined(__cplusplus)
extern "C"
{
#endif /* __cplusplus */

    typedef void (*board_timer_cb)(void);

    void board_init_usb(USB_Type *ptr);

    void board_init_console(void);

    void board_init_uart(UART_Type *ptr);

    uint32_t board_init_uart_clock(UART_Type *ptr);

    void board_init_clock(void);

    void board_delay_us(uint32_t us);

    void board_delay_ms(uint32_t ms);

    void board_led1_on(void);

    void board_led1_off(void);

    void board_led2_on(void);

    void board_led2_off(void);

#if defined(__cplusplus)
}
#endif /* __cplusplus */
#endif /* _HPM_BOARD_H */
